cwg19/ECE-388-Fall-2020/software/conglom/prototype_v0/prototype_v0/userinterface.c

#include "userinterface.h"
#include <stdlib.h>

volatile const char* labels[4] = {"Signal:","Voltage:","Frequency:","Phase:"};
volatile const char* units[3] = {" V"," Hz"," deg"};
volatile const char* signals[4] = {"sine","cosine","square","triangle"};

volatile uint32_t frequency = 0;
volatile uint16_t phase = 0;
volatile int8_t voltage = 0;
volatile uint8_t signal = 0;

extern void lcd_backlight(char on);

extern volatile uint8_t mode;
extern volatile uint8_t modeLast;

void uiInit(void) {
	rotaryInit();
	LCD_I2C_DDR &= ~((1<<LCD_I2C_SCL) | (1<<LCD_I2C_SDA));
	LCD_I2C_PORT |= (1<<LCD_I2C_SCL) | (1<<LCD_I2C_SDA);
	lcd_init(LCD_ON_DISPLAY);
	lcd_backlight(0);
	_delay_ms(500);
	lcd_backlight(1);
	_delay_ms(500);
	displayRefresh();
}

void clearScreen(void) {
	lcd_clrscr();
	_delay_ms(10);
}



void clearLine(unsigned char y) {
	lcd_gotoxy(0,y);
	lcd_puts("                    ");
}

void clearSpace(unsigned char x1,unsigned char x2, unsigned char y) {
	for (uint8_t i = x1; i < x2; i++) {
		lcd_gotoxy(i,y);
		lcd_puts(" ");
	}
	lcd_gotoxy(x1,y);
}

void displayRefresh(void) {
	char val[10];
	if (mode != modeLast) {
		clearScreen();
		lcd_puts(labels[mode]);
	}
	else
		clearLine(1);
	lcd_gotoxy(0,1);
	if (mode == MODE_SIGNAL)
		lcd_puts(signals[signal]);
	else {
		if (mode == MODE_VOLTAGE)
			itoa(voltage,val,10);
		else if (mode == MODE_FREQUENCY)
			itoa(frequency,val,10);
		else if (mode == MODE_PHASE)
			itoa(phase,val,10);
		lcd_puts(val);
		lcd_puts(units[mode-1]);
	}
	val[0] = '\0';
}
